GonzagaEagles16/Boston/Boston - Current design/3D printed version/Bottom/Artwork files (courtesy OpenStreetMap)/boston-streets-14.png

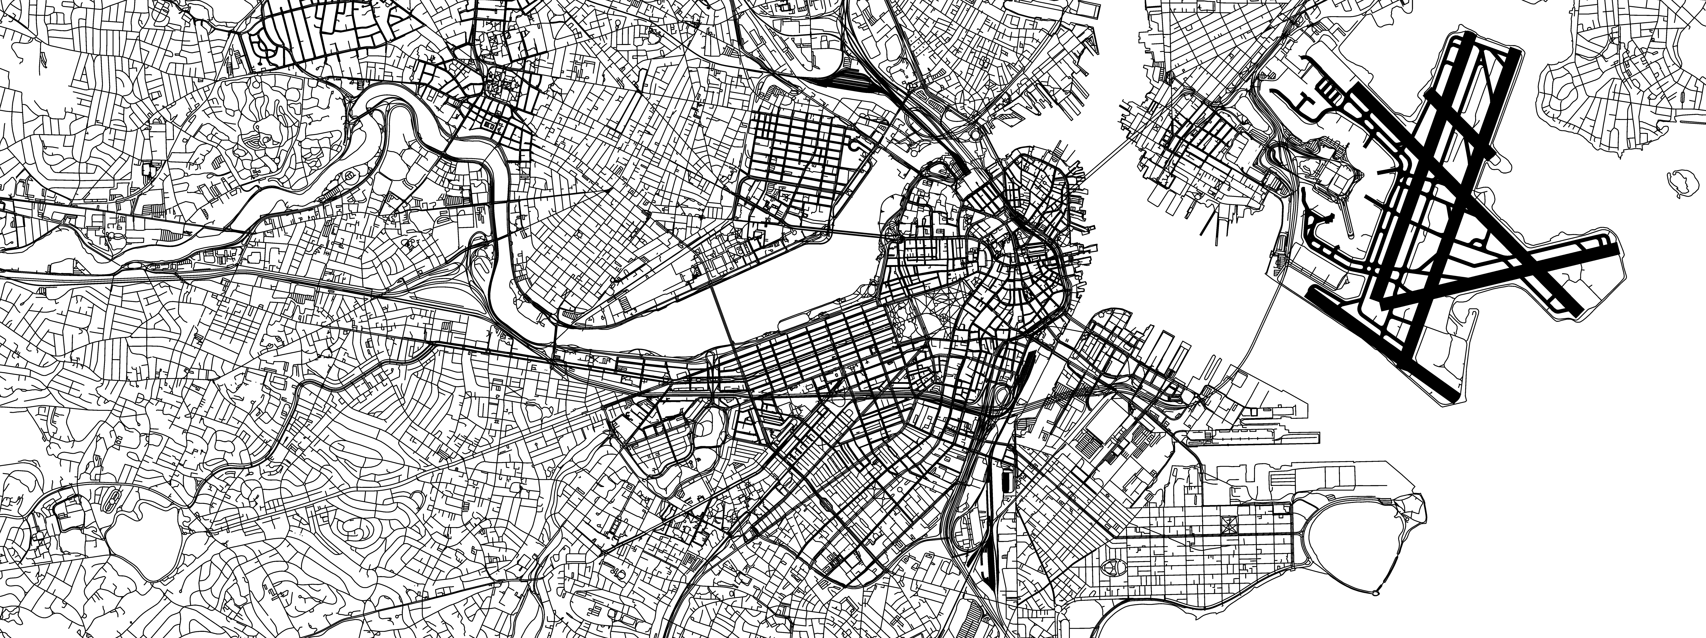
Boston - Current design/3D printed version/Bottom/Artwork files (courtesy OpenStreetMap)/boston-streets-14.png
